DvidMakesThings/HW_BladeCore-M54C/src/HardwareDesign/1.0.0/Images/BladeCore-M54C_Bottom.png

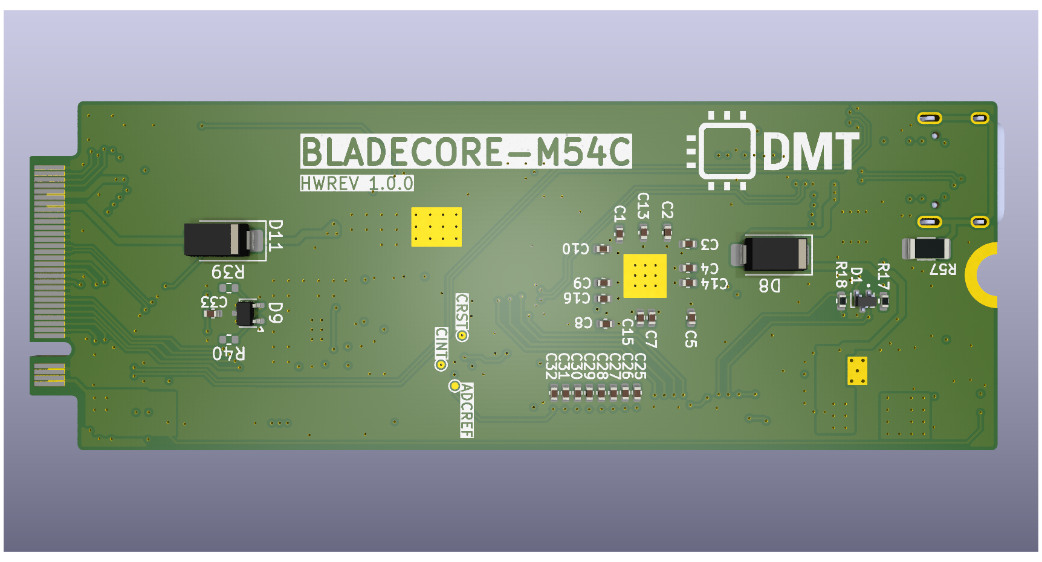
src/HardwareDesign/1.0.0/Images/BladeCore-M54C_Bottom.png
