DvidMakesThings/HW_BladeCore-M54C/src/HardwareDesign/M54-DevBoard_1.0.0/Images/3D/M54-DevBoard_1.0.0-2.png

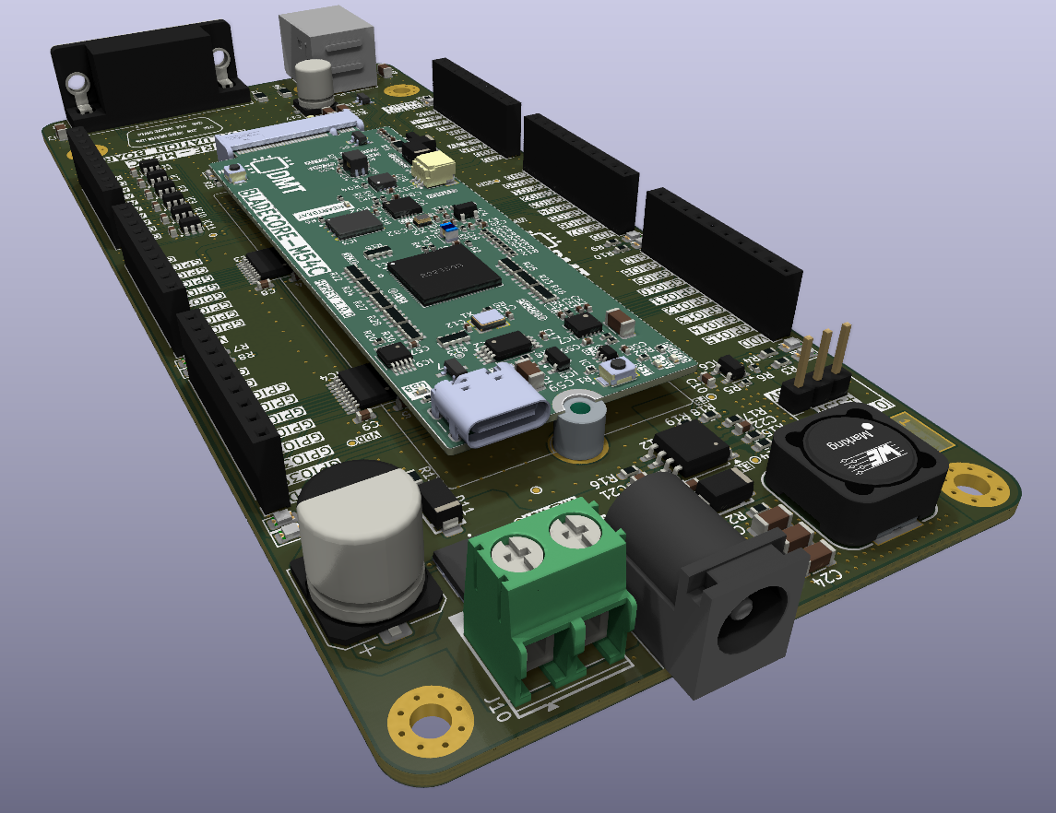
src/HardwareDesign/M54-DevBoard_1.0.0/Images/3D/M54-DevBoard_1.0.0-2.png
