DvidMakesThings/HW_BladeCore-M54C/src/Software/RTOS/_can_schematic.png

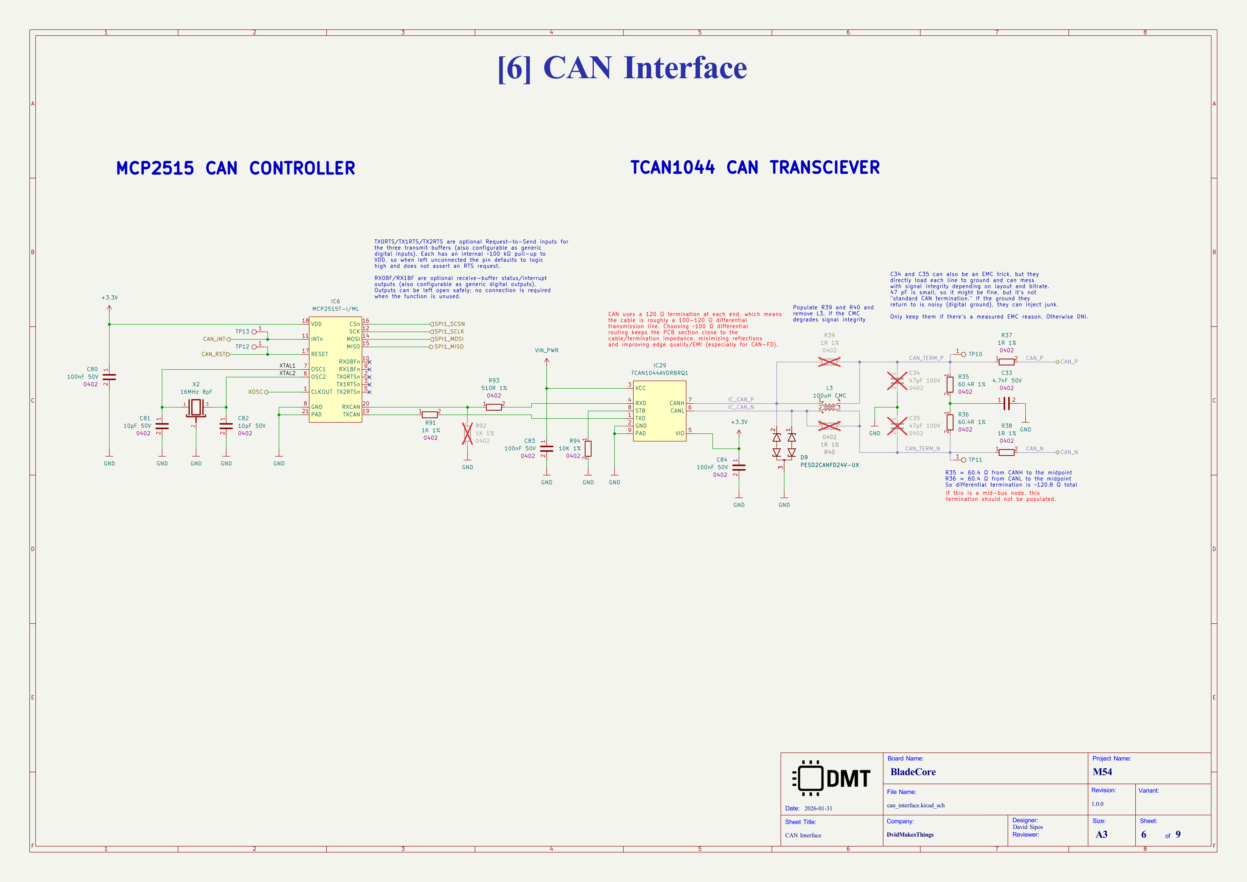
src/Software/RTOS/_can_schematic.png
