DvidMakesThings/HW_BladeCore-M54C/images/DS1Z_QuickPrint7.png

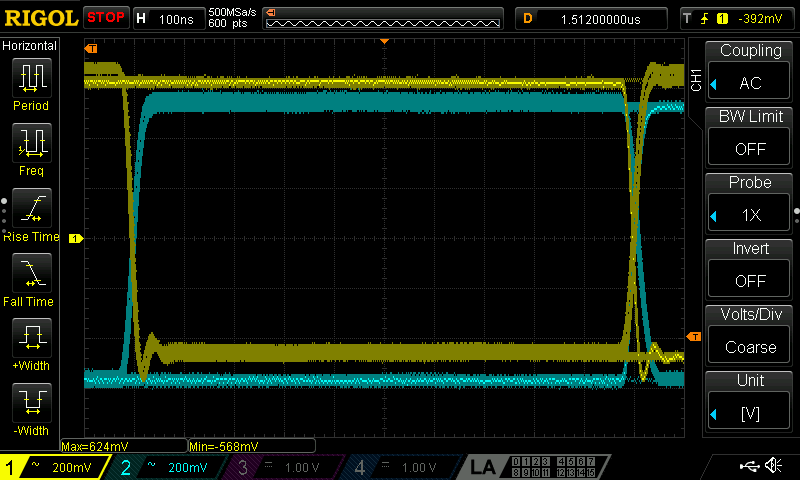
images/DS1Z_QuickPrint7.png
